jbmorley/charger/wood/top/top-small-diameter.dxf

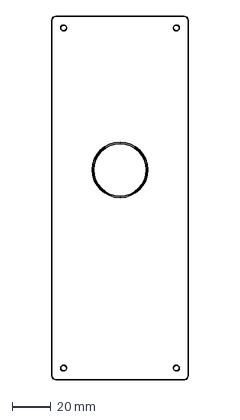
[picture p16: CAD file, 2019-07-13]
wood/top/top-small-diameter.dxf
70.0 x 186.9 mm
