jbmorley/charger/iterations/2019-06-05-acrylic/layer-3.dxf

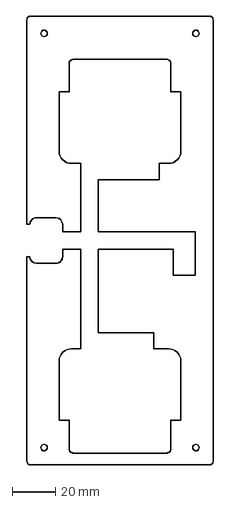
[picture p17: CAD file, 2019-06-05]
iterations/2019-06-05-acrylic/layer-3.dxf
86.0 x 206.9 mm
