jbmorley/charger/wood/body/dxf/botcuts.dxf

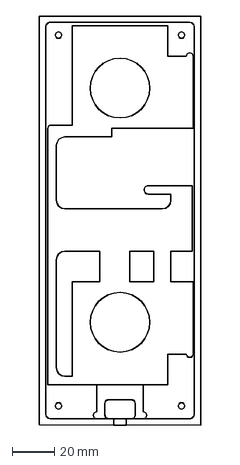
[picture p18: CAD file, 2019-07-04]
wood/body/dxf/botcuts.dxf
76.0 x 192.9 mm
