jbmorley/charger/wood/top/top.dxf

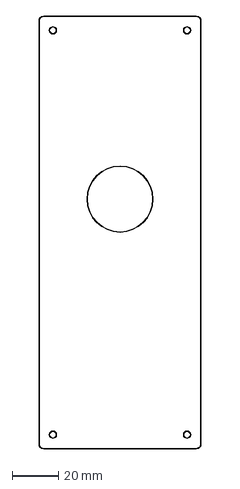
[picture p19: CAD file, 2019-07-13]
wood/top/top.dxf
70.0 x 186.9 mm
