jbmorley/charger/iterations/2019-06-05-acrylic/layer-1.dxf

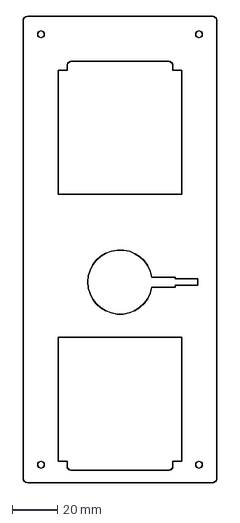
[picture p20: CAD file, 2019-06-05]
iterations/2019-06-05-acrylic/layer-1.dxf
86.0 x 206.9 mm
