jbmorley/charger/wood/body/dxf/bottom-cuts.dxf

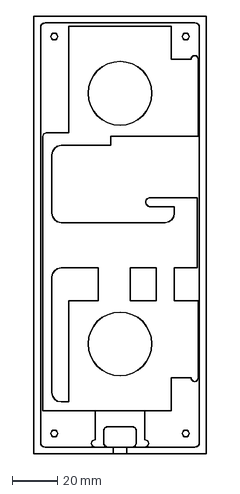
[picture p21: CAD file, 2019-07-03]
wood/body/dxf/bottom-cuts.dxf
76.0 x 192.9 mm
