jbmorley/charger/iterations/2019-06-05-acrylic/layer-4.dxf

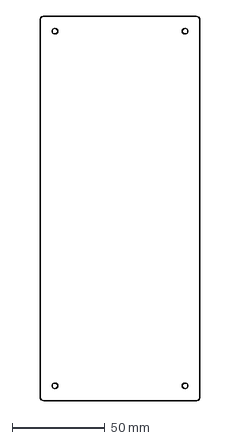
[picture p22: CAD file, 2019-06-03]
iterations/2019-06-05-acrylic/layer-4.dxf
86.0 x 206.9 mm
